David-Jackson/TheFin/Files/STLs/Tertiary Color/Short Plunger Cup.STL

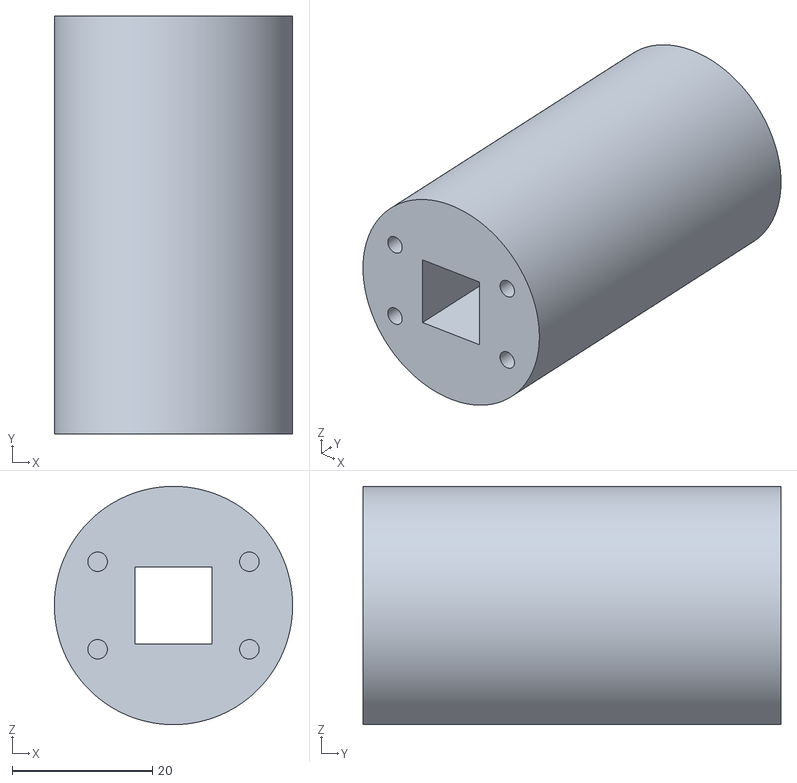
[picture p15: CAD file, 2022-12-16]
Files/STLs/Tertiary Color/Short Plunger Cup.STL
34.0 x 59.7 x 34.0
