David-Jackson/TheFin/Files/STLs/Primary Color/Ram Brace.STL

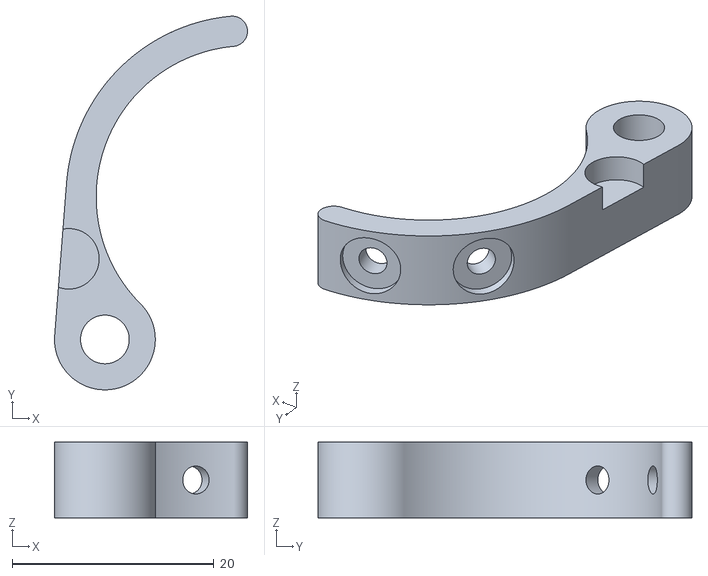
[picture p16: CAD file, 2022-12-16]
Files/STLs/Primary Color/Ram Brace.STL
19.1 x 37.1 x 7.50
