David-Jackson/TheFin/Files/STLs/Secondary Color/Turn Around Spacer.STL

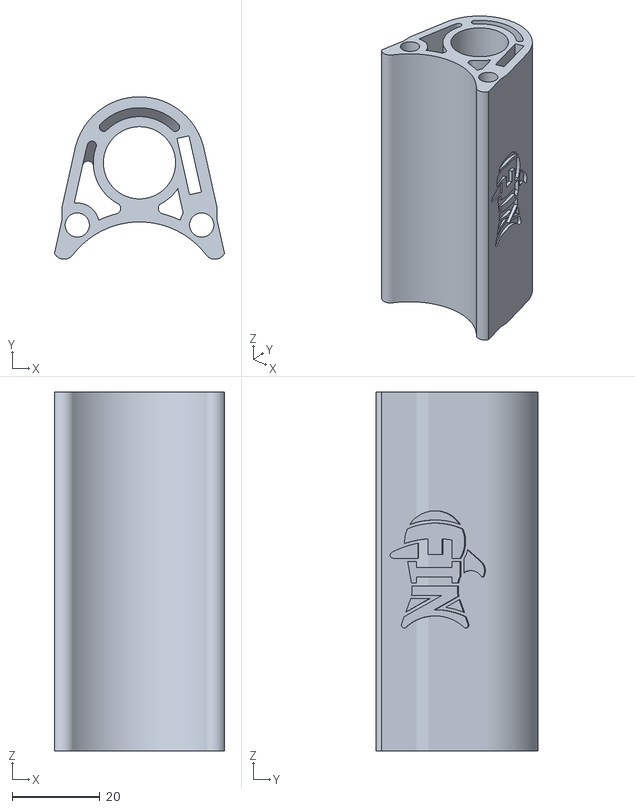
[picture p17: CAD file, 2022-12-20]
Files/STLs/Secondary Color/Turn Around Spacer.STL
38.6 x 36.9 x 81.6
