David-Jackson/TheFin/Files/STLs/Secondary Color/Fronter Spacer.STL

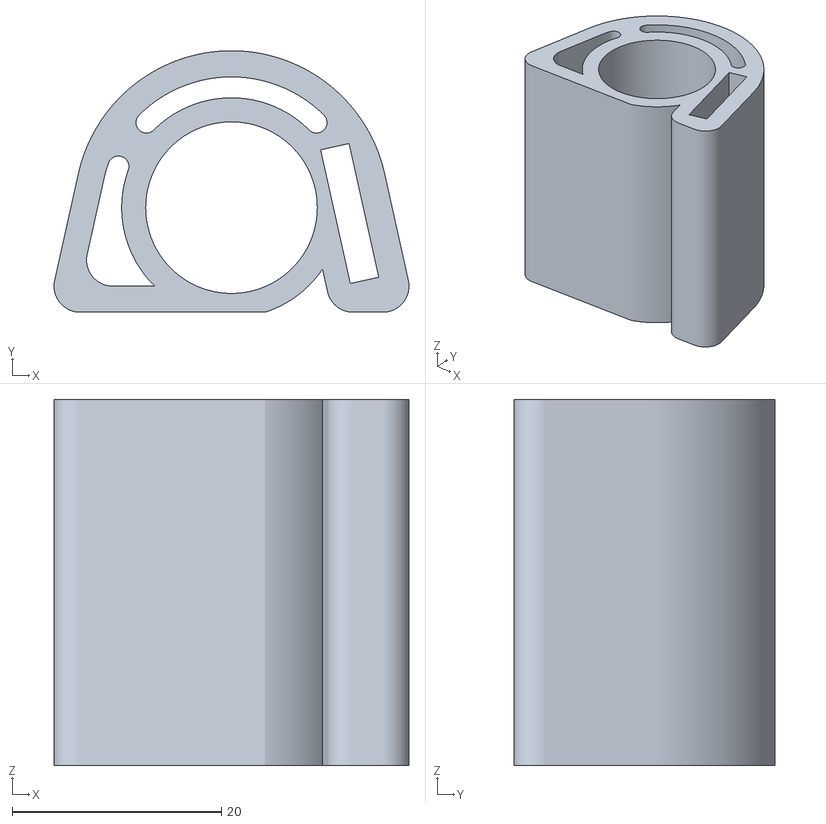
[picture p19: CAD file, 2022-12-16]
Files/STLs/Secondary Color/Fronter Spacer.STL
33.9 x 25.0 x 35.0
