David-Jackson/TheFin/Files/STLs/Tertiary Color/Plunger Catch Cylinder.STL

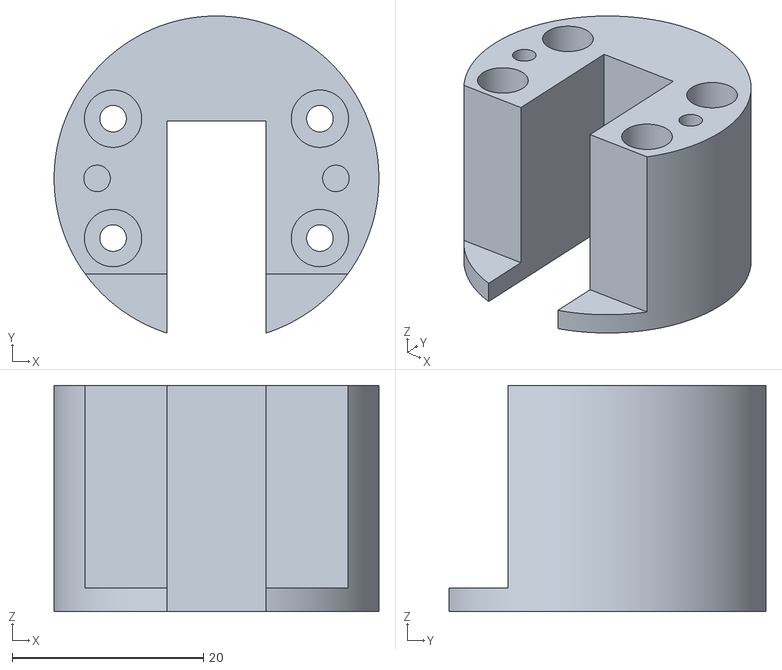
[picture p21: CAD file, 2022-12-16]
Files/STLs/Tertiary Color/Plunger Catch Cylinder.STL
34.0 x 33.2 x 23.7
