David-Jackson/TheFin/Files/STLs/Tertiary Color/Plunger Catch.STL

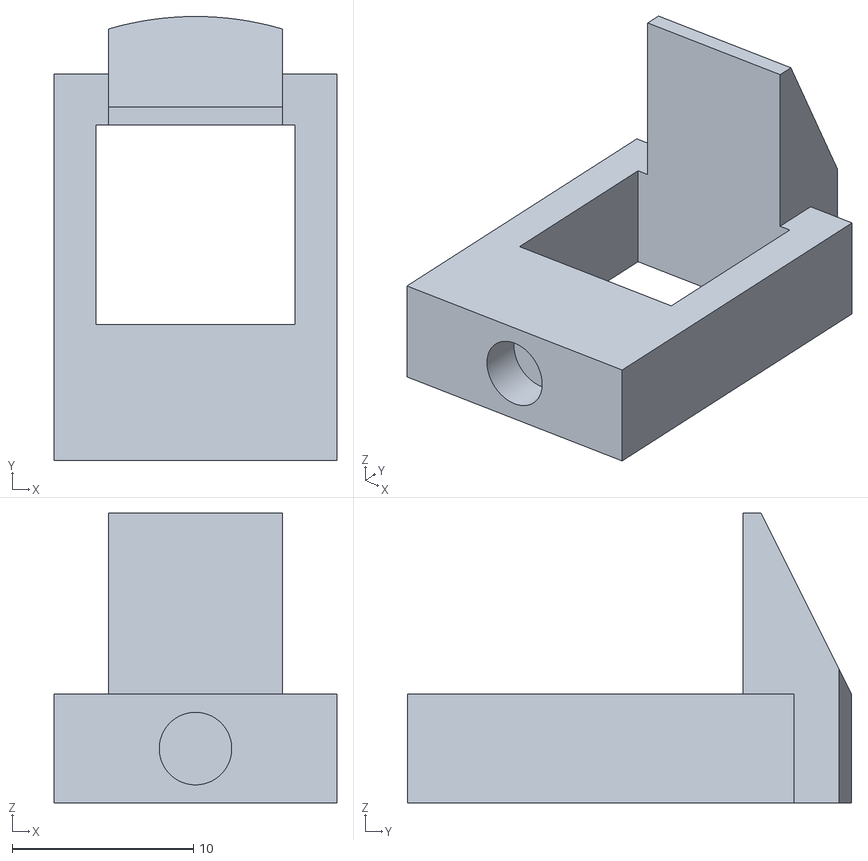
[picture p22: CAD file, 2022-12-16]
Files/STLs/Tertiary Color/Plunger Catch.STL
15.6 x 24.5 x 16.0
